kbob/MinimumViableSynth/Front Panel/archive/bob-synth-full-somevec-0.4.pdf

### Filter

### Filter Envelope

### Amp Envelope

### LFO 1

Assign Amount Speed

### LFO 2

Assign Amount Speed

### Controllers

Velocity
Mod Wheel
Aftertouch
Other
Assign Amount

### Oscillator 1

Amount Pitch Width

### Oscillator 2

Amount Pitch Width

### Noise

White
Pink
Red
Amount

### Mix

Mix
Ring Mod
Hard Sync

# Minimum Viable Synth

Low Pass
High Pass
Off
Key Track Drive Resonance Cutoff

### Envelope 1

Release Sustain Decay Attack Amount Assign

Release Sustain Decay Attack Amount

### Amp

Release Sustain Decay Attack Master Volume
