kbob/MinimumViableSynth/Front Panel/archive/bob-synth-both-0.1.pdf

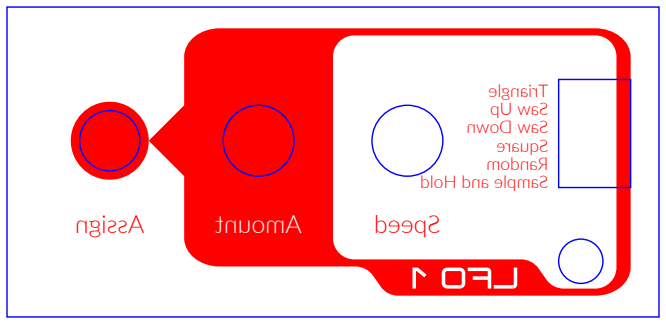
[picture p4: figure]
LFO 1; Triangle Saw Up Saw Down Square Random Sample and Hold; Assign Amount Speed
