kbob/MinimumViableSynth/Front Panel/archive/bob-synth-detail-both-0.1.pdf

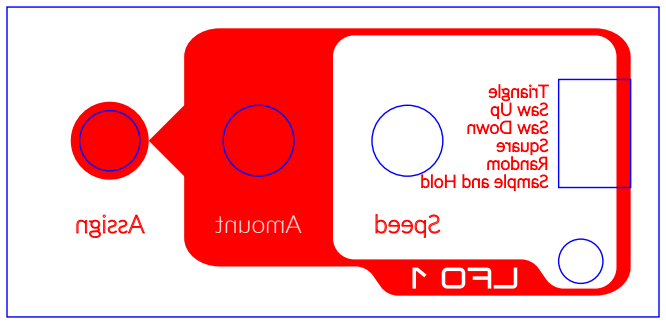
[picture p5: figure]
LFO 1; Triangle Saw Up Saw Down Square Random Sample and Hold; Assign Amount Speed
