kbob/MinimumViableSynth/Front Panel/archive/bob-synth-engrave-0.2.pdf

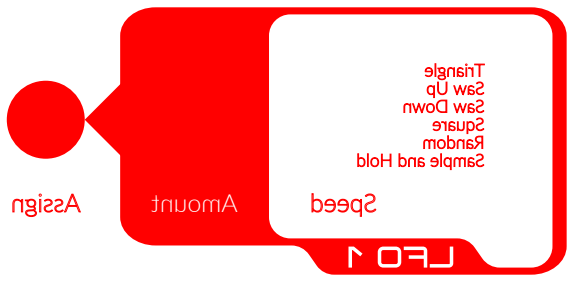
[picture p6: figure]
LFO 1; Triangle Saw Up Saw Down Square Random Sample and Hold; Assign Amount Speed
