kbob/MinimumViableSynth/Front Panel/archive/bob-synth-detail-all-0.3.pdf

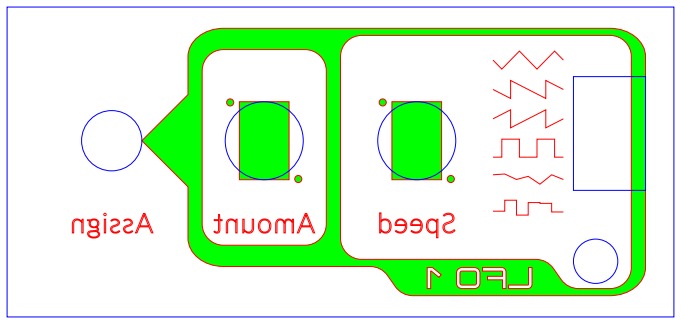
[picture p12: figure]
LFO 1; Assign Amount Speed
