kbob/MinimumViableSynth/Front Panel/archive/bob-synth-detail-allvec-0.3.pdf

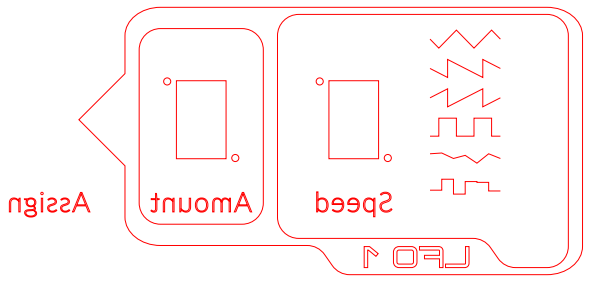
[picture p13: figure]
LFO 1; Assign Amount Speed
