kbob/MinimumViableSynth/Front Panel/archive/bob-synth-detail-art-0.3.pdf

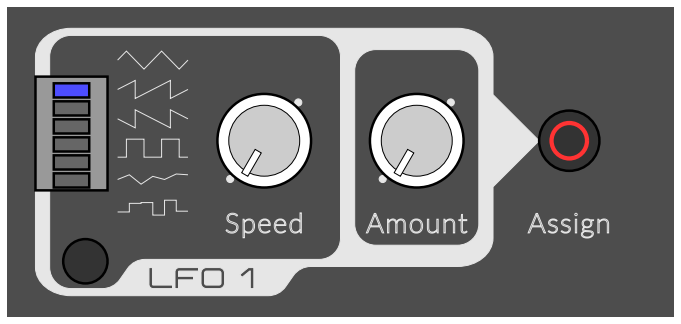
[picture p14: figure]
LFO 1; Speed; Amount; Assign
