kbob/MinimumViableSynth/Front Panel/archive/bob-synth-detail-cut-0.3.pdf

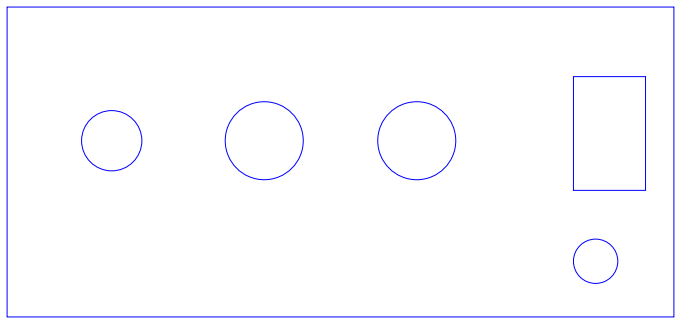
[picture p15: figure]
