kbob/MinimumViableSynth/Front Panel/archive/bob-synth-detail-engrave-0.3.pdf

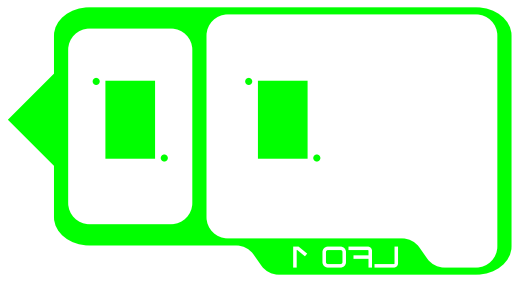
[picture p16: figure]
LFO 1; Assign Amount Speed
