kbob/MinimumViableSynth/Front Panel/archive/bob-synth-cut-0.2.pdf

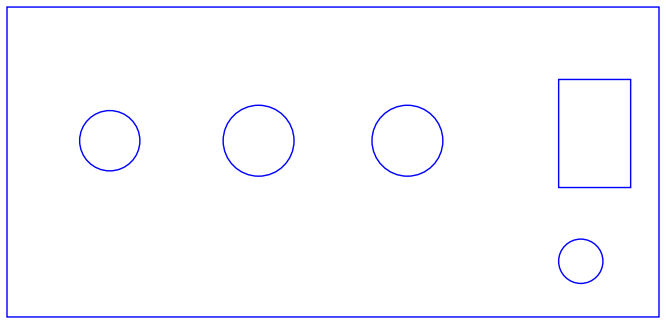
[picture p17: figure]
