kbob/MinimumViableSynth/Front Panel/archive/bob-synth-full-cut-0.3.pdf

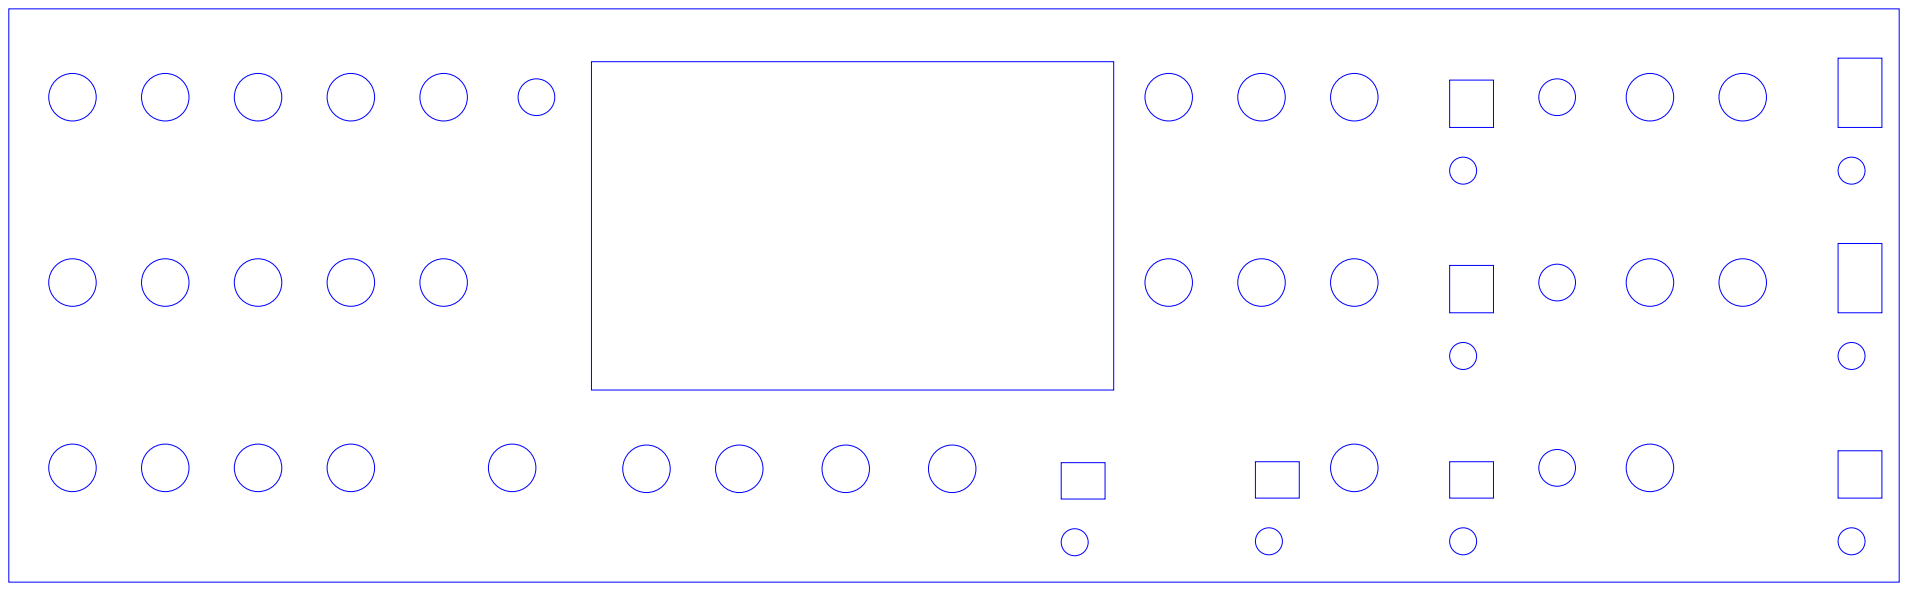
[picture p25: page 1]
