kbob/MinimumViableSynth/Firmware/Master/src/spi-proto.c

#include "spi-proto.h"

#include <assert.h>
#include <stdio.h>
#include <string.h>

#include <libopencm3/cm3/cortex.h>
#include <libopencm3/cm3/nvic.h>

#include "anim.h"
#include "config.h"
#include "delay.h"
#include "spi.h"
#include "state.h"
#include "systick.h"

#define MAX_SPI_PACKET_SIZE 32

static const uint8_t STX = '\02';
static const uint8_t ETX = '\03';
static const uint8_t SYN = '\26';

// active_modules is a hack to allow turning the synth on one module at a time.
static const size_t active_modules[] = {
    M_LFO1,
    M_LFO2,
    M_CTLRS,
    M_OSC1,
    M_OSC2,
    M_NOIS,
    M_MIX,
    // M_FILT,
    // M_ENV1,
    // M_ENV2,
    // M_ENV3,
};
static const size_t active_module_count = (&active_modules)[1] - active_modules;

typedef uint8_t spi_buf[MAX_SPI_PACKET_SIZE];

typedef enum SPI_state {
    SS_IDLE,
    SS_START,
    SS_ACTIVE,
    SS_GROUP_DONE,
    SS_POSTPROCESSING,
} SPI_state;

typedef struct SPI_stats {
    uint32_t ok_count[MODULE_COUNT];
    uint32_t fail_count[MODULE_COUNT];
    uint32_t skip_count;
} SPI_stats;

// XXX move this where other drivers can use it.
#define DMA_SECTION __attribute((section(".system_ram")))
//#define DMA_SECTION

static volatile SPI_state sp_state;
static volatile int current_grp_idx;
static spi_buf outgoing_packets[MODULE_COUNT] DMA_SECTION;
static spi_buf incoming_packets[MODULE_COUNT] DMA_SECTION;
static slave_state slave_states[MODULE_COUNT];
static SPI_stats stats;
static SPI_slave_state_handler *slave_state_handler;
static void *handler_data;

static void module_to_spi(size_t   module_index,
                          uint8_t *spi_group_out,
                          uint8_t *spi_bus_out)
{
    assert(module_index < MODULE_COUNT);
    const module_config *mcp = &sc.sc_modules[module_index];
    if (spi_group_out)
        *spi_group_out = mcp->mc_SPI_group;
    if (spi_bus_out)
        *spi_bus_out = mcp->mc_SPI_bus;
}

size_t spi_to_module(int spi_group, int spi_bus)
{
    static size_t spi2mod[SPI_GROUP_COUNT][SPI_BUS_RANGE];
    static bool initialized;

    if (!initialized) {
        for (size_t i = 0; i < MODULE_COUNT; i++) {
            uint8_t grp, bus;
            module_to_spi(i, &grp, &bus);
            spi2mod[grp][bus] = i;
        }
        initialized = true;
    }
    assert(0 <= spi_group && spi_group < SPI_GROUP_COUNT);
    assert(0 <= spi_bus && spi_bus < SPI_BUS_RANGE);
    return spi2mod[spi_group][spi_bus];
}

int active_spi_groups(uint8_t index)
{
    static uint8_t active_groups[SPI_GROUP_COUNT];
    static size_t active_group_count;

    if (!active_group_count) {
        bool active[SPI_GROUP_COUNT];
        memset(active, 0, sizeof active);
        for (size_t i = 0; i < active_module_count; i++) {
            uint8_t grp, bus;
            module_to_spi(active_modules[i], &grp, &bus);
            active[grp] = true;
        }
        for (size_t g = 0; g < SPI_GROUP_COUNT; g++)
            if (active[g])
                active_groups[active_group_count++] = g;
    }

    if (index < active_group_count)
        return active_groups[index];
    else
        return NO_GROUP;
}

int active_spi_buses(uint8_t group, uint8_t index)
{
    static uint8_t active_buses[SPI_GROUP_COUNT][SPI_BUS_COUNT];
    static size_t active_bus_count[SPI_GROUP_COUNT];
    static bool initialized;

    if (!initialized) {
        bool active[SPI_GROUP_COUNT][SPI_BUS_RANGE];
        memset(active, 0, sizeof active);
        for (size_t i = 0; i < active_module_count; i++) {
            uint8_t grp, bus;
            module_to_spi(active_modules[i], &grp, &bus);
            active[grp][bus] = true;
        }
        for (size_t g = 0; g < SPI_GROUP_COUNT; g++)
            for (size_t b = 0; b < SPI_BUS_RANGE; b++)
                if (active[g][b]) {
                    assert(active_bus_count[g] < SPI_BUS_COUNT);
                    active_buses[g][active_bus_count[g]++] = b;
                }
        initialized = true;
    }

    if (group >= SPI_GROUP_COUNT)
        return NO_GROUP;
    if (index < active_bus_count[group])
        return active_buses[group][index];
    else
        return NO_BUS;
}

static uint16_t fletcher16(const uint8_t *p, size_t count)
{
    uint16_t sum = 0;
    uint16_t sum2 = 0;
    for (size_t i = 0; i < count; i++) {
        sum += p[i];
        if (sum >= 255)
            sum -= 255;
        sum2 += sum;
        if (sum2 >= 255)
            sum2 -= 255;
    }
    return sum2 << 8 | sum;
}

// MOSI message format
//
//   STX : 1 byte
//   config 0 : 1 byte
//     bit 0:      c1 = nonzero if choice one lit
//     bit 1:      c2 = nonzero if choice two lit
//     bit 2:      c3 = nonzero if choice three lit
//     bit 3:      c4 = nonzero if choice four lit
//     bit 4:      c5 = nonzero if choice five lit
//     bit 5:      c6 = nonzero if choice six lit
//     bit 6:       (not used)
//     bit 7:      ap = nonzero if assign LED lit
//   config 1: 1 byte
//     bits 0-2:   np = number of pixels
//     bits 3-5:   na = number of analog inputs
//     bits 6-7:   unused
//   choice LED pwm: 1 byte per lit choice
//   assign LED pwm: 1 byte
//   pixels: 3 * np bytes
//     1st: title
//     2nd - np'th: knobs
//     red, green, blue order
//   checksum : 2 bytes
//   ETX : 1 byte

static size_t assemble_outgoing_packet(spi_buf packet, size_t module_index)
{
    const module_config *mcp = &sc.sc_modules[module_index];
    const module_state *msp = &ss.ss_modules[module_index];

    // These variables are copied into the packet.
    uint8_t cfg0 = 0;
    uint8_t cfg1 = 0;
    uint8_t pwm[MAX_CHOICES + MAX_ASSIGNS];
    size_t pwm_count = 0;
    uint8_t pixels[MAX_PIXELS][3];
    size_t pixel_count = 0;

    // Collect the info.
    if (mcp->mc_has_choice) {
        uint8_t first = 6 - mcp->mc_choice.cc_count;
        cfg0 |= 1 << (first + msp->ms_choice.cs_value);
        pwm[pwm_count++] = anim_choice_brightness(module_index);
    }

    if (mcp->mc_has_assign) {
        cfg0 |= 1 << 7;
        pwm[pwm_count++] = anim_assign_brightness(module_index);
    }
    
    packed_RGB rgb = anim_module_color(module_index);
    uint8_t pix = mcp->mc_LED;
    pixels[pix][0] = rgb >> 16 & 0xFF;
    pixels[pix][1] = rgb >>  8 & 0xFF;
    pixels[pix][2] = rgb >>  0 & 0xFF;

    if (mcp->mc_flags & MCF_CTLRS)
        pixel_count = 2;
    else
        pixel_count = 1 + mcp->mc_knob_count;
    cfg1 = pixel_count | mcp->mc_knob_count << 3;
    
    for (size_t ki = 0; ki < mcp->mc_knob_count; ki++) {
        const knob_config *kcp = &mcp->mc_knobs[ki];
        if (kcp->kc_name) {     // if knob exists...
            packed_RGB rgb = anim_knob_color(module_index, ki);
            uint8_t pix = kcp->kc_LED;
            pixels[pix][0] = rgb >> 16 & 0xFF;
            pixels[pix][1] = rgb >>  8 & 0xFF;
            pixels[pix][2] = rgb >>  0 & 0xFF;
        }
    }

    // Assemble the packet.
    uint8_t *p = packet;
    *p++ = STX;
    *p++ = cfg0;
    *p++ = cfg1;
    for (size_t i = 0; i < pwm_count; i++)
        *p++ = pwm[i];
    for (size_t i = 0; i < pixel_count; i++) {
        *p++ = pixels[i][0];
        *p++ = pixels[i][1];
        *p++ = pixels[i][2];
    }
    uint16_t cksum = fletcher16(packet + 1, p - packet - 1);
    *p++ = cksum >> 8;
    *p++ = cksum & 0xFF;
    *p++ = ETX;
    *p++ = SYN;
    assert(p - packet <= MAX_SPI_PACKET_SIZE);

    return p - packet;
}

// MISO message format
//
//   STX : 1 byte
//   switches: 1 byte
//     bit 0: c0 clicked
//     bit 1: assign clicked
//     bit 2: destination button 1 clicked
//     bit 3: destination button 2 clicked
//     bit 4: destination button 3 clicked
//     bit 5: destination button 4 clicked
//   analog: 1 byte
//     bit 0: analog 1 changed
//     bit 1: analog 2 changed
//     bit 2: analog 3 changed
//     bit 3: analog 4 changed
//     bit 4: analog 5 changed
//   analog values:  1 byte per changed value
//   checksum : 2 bytes
//   ETX : 1 byte

static bool check_buttons(uint8_t button_mask, size_t module_index)
{
    const module_config *mod = &sc.sc_modules[module_index];
    if ((button_mask & SBB_CHOICE) && !mod->mc_has_choice)
        return false;
    if ((button_mask & SBB_ASSIGN) && !mod->mc_has_assign)
        return false;
    for (size_t i = mod->mc_knob_count; i < MAX_KNOBS; i++)
        if ((button_mask & 1 << (i + 2)))
            return false;
    return true;
}

static bool check_analog(uint8_t analog_mask, size_t module_index)
{
    const module_config *mod = &sc.sc_modules[module_index];
    for (int i = 0; i < MAX_KNOBS; i++)
        if (analog_mask & (1 << i) &&
            (i >= mod->mc_knob_count || !mod->mc_knobs[i].kc_has_button))
            return false;
    return true;
}

static bool parse_incoming_packet(spi_buf const packet,
                                  size_t        count,
                                  size_t        module_index,
                                  slave_state  *state_out)
{
#if 0
    #define PARSE_DBG(fmt, ...)                             \
        (printf("%s: " fmt "\n",                            \
                sc.sc_modules[module_index].mc_name,        \
                __VA_ARGS__))
#else
    #define PARSE_DBG(fmt, ...) ((void)0)
#endif

    if (count < 6) {
        PARSE_DBG("count = %u < 6, fail", count);
        return false;
    }
    if (packet[0] != STX) {
        PARSE_DBG("packet[0] = %#o != STX", packet[0]);
        return false;
    }
    size_t len = 6;             // 6 bytes: STX bmask amask chk chk ETX
    uint8_t bmask = packet[1];
    uint8_t amask = packet[2];
    for (uint8_t i = 1; i; i <<= 1)
        if (amask & i)
            len++;
    if (count < len) {
        PARSE_DBG("received %u bytes, expected %u bytes", count, len);
        return false;
    }
    uint16_t rx_chk = (uint16_t)packet[len - 3] << 8 | packet[len - 2];
    uint16_t cc_chk = fletcher16(packet + 1, len - 4);
    if (rx_chk != cc_chk) {
        PARSE_DBG("chk: got %#x, not %#x", rx_chk, cc_chk);
        return false;
    }
    if (packet[len - 1] != ETX) {
        PARSE_DBG("packet[%u] = %#o, expected ETX", len - 1, packet[len - 1]);
        return false;
    }
    if (!check_buttons(bmask, module_index)) {
        PARSE_DBG("bmask %#x invalid", bmask);
        return false;
    }
    if (!check_analog(amask, module_index)) {
        PARSE_DBG("amask %#x invalid", amask);
        return false;
    }

    // Populate the slave_state.
    state_out->ss_is_valid = true;
    state_out->ss_buttons = bmask;
    state_out->ss_analog_mask = amask;
    const uint8_t *p = packet + 3;
    for (int i = 0; i < MAX_KNOBS; i++)
        if (amask & (1 << i))
            state_out->ss_analog_values[i] = *p++;
    return true;
}

static void start_SPI_group(int grp)
{
    spi_select_group(grp);
    delay_usec(20);
    int bus;
    for (int i = 0; (bus = active_spi_buses(grp, i)) != NO_BUS; i++) {
        size_t mod_idx = spi_to_module(grp, bus);
        size_t bytes_out =
            assemble_outgoing_packet(outgoing_packets[mod_idx], mod_idx);
        spi_start_transfer(bus,
                           outgoing_packets[mod_idx],
                           incoming_packets[mod_idx],
                           bytes_out);
    }
}

static void stop_SPI_group(int grp)
{
    int bus;
    for (int i = 0; (bus = active_spi_buses(grp, i)) != NO_BUS; i++)
        spi_finish_transfer(bus);
    delay_usec(20);
    spi_deselect_group(grp);
}

static void process_SPI_group(int grp)
{
    int bus;
    for (int i = 0; (bus = active_spi_buses(grp, i)) != NO_BUS; i++) {
        size_t mod_idx = spi_to_module(grp, bus);
        bool ok = parse_incoming_packet(incoming_packets[mod_idx],
                                        sizeof incoming_packets[mod_idx],
                                        mod_idx,
                                        &slave_states[mod_idx]);
        if (ok)
            stats.ok_count[mod_idx]++;
        else
            stats.fail_count[mod_idx]++;
    }
}

static void postprocess_SPI(void)
{
    if (slave_state_handler) {
        for (size_t i = 0; i < MODULE_COUNT; i++) {
            const slave_state *ss = &slave_states[i];
            if (ss->ss_is_valid)
                (*slave_state_handler)(i, &slave_states[i], handler_data);
        }
    }
}

// This is the main event handler for the SPI proto task.
void exti0_isr(void)
{
    switch (sp_state) {

    case SS_START:
        memset(outgoing_packets, 0, sizeof outgoing_packets);
        memset(incoming_packets, 0, sizeof incoming_packets);
        memset(slave_states, 0, sizeof slave_states);
        current_grp_idx = -1;
        anim_update(system_millis);
        /* FALLTHRU */

    case SS_GROUP_DONE:;
        // N.B., we start the next SPI group running before
        // we parse the reply messages from the current group.
        int prev_grp_idx = current_grp_idx;
        current_grp_idx++;
        int current_grp = active_spi_groups(current_grp_idx);
        if (prev_grp_idx != -1)
            stop_SPI_group(active_spi_groups(prev_grp_idx));
        if (current_grp != NO_GROUP) {
            sp_state = SS_ACTIVE;
            start_SPI_group(current_grp);
        }
        if (prev_grp_idx != -1) {
            int prev_grp = active_spi_groups(prev_grp_idx);
            process_SPI_group(prev_grp);
        }
        if (current_grp == NO_GROUP) {
            sp_state = SS_POSTPROCESSING;
            postprocess_SPI();
            sp_state = SS_IDLE;
        }
        break;

    case SS_ACTIVE:
    case SS_IDLE:
    case SS_POSTPROCESSING:
        assert(!"Unexpected SPI state");
        break;
    }
}

static void handle_systick(uint32_t millis)
{
    if (sp_state == SS_IDLE) {
        sp_state = SS_START;
        nvic_generate_software_interrupt(NVIC_EXTI0_IRQ);
    } else {
        stats.skip_count++;
    }
}

static void handle_SPI_completion(void)
{
    if (sp_state == SS_ACTIVE) {
        sp_state = SS_GROUP_DONE;
        nvic_generate_software_interrupt(NVIC_EXTI0_IRQ);
    }
}

void SPI_proto_setup(void)
{
    spi_register_completion_handler(handle_SPI_completion);
    sp_state = SS_IDLE;
    nvic_set_priority(NVIC_EXTI0_IRQ, 0xFF);
    nvic_enable_irq(NVIC_EXTI0_IRQ);
    register_systick_handler(handle_systick);
}

void SPI_proto_register_slave_state_handler(SPI_slave_state_handler *handler,
                                            void *user_data)
{
    slave_state_handler = handler;
    handler_data = user_data;
}

void SPI_proto_report_and_clear_stats(void)
{
    bool interrupts_are_masked = cm_is_masked_interrupts();
    cm_disable_interrupts();

    SPI_stats tmp = stats;
    memset(&stats, 0, sizeof stats);

    if (!interrupts_are_masked)
        cm_enable_interrupts();

    printf("   OK  fail module\n");
    for (size_t i = 0; i < MODULE_COUNT; i++) {
        uint32_t ok = tmp.ok_count[i];
        uint32_t fail = tmp.fail_count[i];
        if (!ok && !fail)
            continue;
        const char *mod_name = sc.sc_modules[i].mc_name;
        printf("%5lu %5lu %s\n", ok, fail, mod_name);
    }
    if (tmp.skip_count)
        printf("skipped %lu\n", tmp.skip_count);
    printf("\n");
}
