kbob/MinimumViableSynth/Firmware/Master/src/usb-midi.c

#include "usb-midi.h"

// Based heavily on usbmidi.c in libopencm3-examples, which is
//  * Copyright (C) 2014 Daniel Thompson <daniel@redfelineninja.org.uk>
//  * Copyright (C) 2015 Piotr Esden-Tempski <piotr@esden.net>
// and licensed under the LGPL.

/*
 * All references in this file come from Universal Serial Bus Device Class
 * Definition for MIDI Devices, release 1.0.
 */

#include <assert.h>
#include <stdio.h>
#include <string.h>

#include <libopencm3/cm3/cortex.h>
#include <libopencm3/cm3/nvic.h>

#include <libopencm3/usb/usbd.h>
#include <libopencm3/usb/audio.h>
#include <libopencm3/usb/midi.h>

#include <libopencm3/stm32/rcc.h>

#include "gpio.h"
#include "midi-defs.h"

/*
 * Table B-1: MIDI Adapter Device Descriptor
 */
static const struct usb_device_descriptor dev = {
	.bLength = USB_DT_DEVICE_SIZE,
	.bDescriptorType = USB_DT_DEVICE,
	.bcdUSB = 0x0200,    /* was 0x0110 in Table B-1 example descriptor */
	.bDeviceClass = 0,   /* device defined at interface level */
	.bDeviceSubClass = 0,
	.bDeviceProtocol = 0,
	.bMaxPacketSize0 = 64,
	.idVendor = 0x6666,  /* Prototype product vendor ID */
	.idProduct = 0x5119, /* dd if=/dev/random bs=2 count=1 | hexdump */
	.bcdDevice = 0x0100,
	.iManufacturer = 1,  /* index to string desc */
	.iProduct = 2,       /* index to string desc */
	.iSerialNumber = 0,
	.bNumConfigurations = 1,
};

/*
 * Midi specific endpoint descriptors.
 */
static const struct usb_midi_endpoint_descriptor midi_bulk_endp[] = {{
	/* Table B-12: MIDI Adapter Class-specific Bulk OUT Endpoint
	 * Descriptor
	 */
	.head = {
		.bLength = sizeof(struct usb_midi_endpoint_descriptor),
		.bDescriptorType = USB_AUDIO_DT_CS_ENDPOINT,
		.bDescriptorSubType = USB_MIDI_SUBTYPE_MS_GENERAL,
		.bNumEmbMIDIJack = 1,
	},
	.jack[0] = {
		.baAssocJackID = 0x01,
	},
}, {
	/* Table B-14: MIDI Adapter Class-specific Bulk IN Endpoint
	 * Descriptor
	 */
	.head = {
		.bLength = sizeof(struct usb_midi_endpoint_descriptor),
		.bDescriptorType = USB_AUDIO_DT_CS_ENDPOINT,
		.bDescriptorSubType = USB_MIDI_SUBTYPE_MS_GENERAL,
		.bNumEmbMIDIJack = 1,
	},
	.jack[0] = {
		.baAssocJackID = 0x03,
	},
} };

/*
 * Standard endpoint descriptors
 */
static const struct usb_endpoint_descriptor bulk_endp[] = {{
	/* Table B-11: MIDI Adapter Standard Bulk OUT Endpoint Descriptor */
	.bLength = USB_DT_ENDPOINT_SIZE,
	.bDescriptorType = USB_DT_ENDPOINT,
	.bEndpointAddress = 0x01,
	.bmAttributes = USB_ENDPOINT_ATTR_BULK,
	.wMaxPacketSize = 0x40,
	.bInterval = 0x00,

	.extra = &midi_bulk_endp[0],
	.extralen = sizeof(midi_bulk_endp[0])
}, {
	.bLength = USB_DT_ENDPOINT_SIZE,
	.bDescriptorType = USB_DT_ENDPOINT,
	.bEndpointAddress = 0x81,
	.bmAttributes = USB_ENDPOINT_ATTR_BULK,
	.wMaxPacketSize = 0x40,
	.bInterval = 0x00,

	.extra = &midi_bulk_endp[1],
	.extralen = sizeof(midi_bulk_endp[1])
} };

/*
 * Table B-4: MIDI Adapter Class-specific AC Interface Descriptor
 */
static const struct {
	struct usb_audio_header_descriptor_head header_head;
	struct usb_audio_header_descriptor_body header_body;
} __attribute__((packed)) audio_control_functional_descriptors = {
	.header_head = {
		.bLength = sizeof(struct usb_audio_header_descriptor_head) +
			   1 * sizeof(struct usb_audio_header_descriptor_body),
		.bDescriptorType = USB_AUDIO_DT_CS_INTERFACE,
		.bDescriptorSubtype = USB_AUDIO_TYPE_HEADER,
		.bcdADC = 0x0100,
		.wTotalLength =
			   sizeof(struct usb_audio_header_descriptor_head) +
			   1 * sizeof(struct usb_audio_header_descriptor_body),
		.binCollection = 1,
	},
	.header_body = {
		.baInterfaceNr = 0x01,
	},
};

/*
 * Table B-3: MIDI Adapter Standard AC Interface Descriptor
 */
static const struct usb_interface_descriptor audio_control_iface[] = {{
	.bLength = USB_DT_INTERFACE_SIZE,
	.bDescriptorType = USB_DT_INTERFACE,
	.bInterfaceNumber = 0,
	.bAlternateSetting = 0,
	.bNumEndpoints = 0,
	.bInterfaceClass = USB_CLASS_AUDIO,
	.bInterfaceSubClass = USB_AUDIO_SUBCLASS_CONTROL,
	.bInterfaceProtocol = 0,
	.iInterface = 0,

	.extra = &audio_control_functional_descriptors,
	.extralen = sizeof(audio_control_functional_descriptors)
} };

/*
 * Class-specific MIDI streaming interface descriptor
 */
static const struct {
	struct usb_midi_header_descriptor header;
	struct usb_midi_in_jack_descriptor in_embedded;
	struct usb_midi_in_jack_descriptor in_external;
	struct usb_midi_out_jack_descriptor out_embedded;
	struct usb_midi_out_jack_descriptor out_external;
} __attribute__((packed)) midi_streaming_functional_descriptors = {
	/* Table B-6: Midi Adapter Class-specific MS Interface Descriptor */
	.header = {
		.bLength = sizeof(struct usb_midi_header_descriptor),
		.bDescriptorType = USB_AUDIO_DT_CS_INTERFACE,
		.bDescriptorSubtype = USB_MIDI_SUBTYPE_MS_HEADER,
		.bcdMSC = 0x0100,
		.wTotalLength = sizeof(midi_streaming_functional_descriptors),
	},
	/* Table B-7: MIDI Adapter MIDI IN Jack Descriptor (Embedded) */
	.in_embedded = {
		.bLength = sizeof(struct usb_midi_in_jack_descriptor),
		.bDescriptorType = USB_AUDIO_DT_CS_INTERFACE,
		.bDescriptorSubtype = USB_MIDI_SUBTYPE_MIDI_IN_JACK,
		.bJackType = USB_MIDI_JACK_TYPE_EMBEDDED,
		.bJackID = 0x01,
		.iJack = 0x00,
	},
	/* Table B-8: MIDI Adapter MIDI IN Jack Descriptor (External) */
	.in_external = {
		.bLength = sizeof(struct usb_midi_in_jack_descriptor),
		.bDescriptorType = USB_AUDIO_DT_CS_INTERFACE,
		.bDescriptorSubtype = USB_MIDI_SUBTYPE_MIDI_IN_JACK,
		.bJackType = USB_MIDI_JACK_TYPE_EXTERNAL,
		.bJackID = 0x02,
		.iJack = 0x00,
	},
	/* Table B-9: MIDI Adapter MIDI OUT Jack Descriptor (Embedded) */
	.out_embedded = {
		.head = {
			.bLength = sizeof(struct usb_midi_out_jack_descriptor),
			.bDescriptorType = USB_AUDIO_DT_CS_INTERFACE,
			.bDescriptorSubtype = USB_MIDI_SUBTYPE_MIDI_OUT_JACK,
			.bJackType = USB_MIDI_JACK_TYPE_EMBEDDED,
			.bJackID = 0x03,
			.bNrInputPins = 1,
		},
		.source[0] = {
			.baSourceID = 0x02,
			.baSourcePin = 0x01,
		},
		.tail = {
			.iJack = 0x00,
		}
	},
	/* Table B-10: MIDI Adapter MIDI OUT Jack Descriptor (External) */
	.out_external = {
		.head = {
			.bLength = sizeof(struct usb_midi_out_jack_descriptor),
			.bDescriptorType = USB_AUDIO_DT_CS_INTERFACE,
			.bDescriptorSubtype = USB_MIDI_SUBTYPE_MIDI_OUT_JACK,
			.bJackType = USB_MIDI_JACK_TYPE_EXTERNAL,
			.bJackID = 0x04,
			.bNrInputPins = 1,
		},
		.source[0] = {
			.baSourceID = 0x01,
			.baSourcePin = 0x01,
		},
		.tail = {
			.iJack = 0x00,
		},
	},
};

/*
 * Table B-5: MIDI Adapter Standard MS Interface Descriptor
 */
static const struct usb_interface_descriptor midi_streaming_iface[] = {{
	.bLength = USB_DT_INTERFACE_SIZE,
	.bDescriptorType = USB_DT_INTERFACE,
	.bInterfaceNumber = 1,
	.bAlternateSetting = 0,
	.bNumEndpoints = 2,
	.bInterfaceClass = USB_CLASS_AUDIO,
	.bInterfaceSubClass = USB_AUDIO_SUBCLASS_MIDISTREAMING,
	.bInterfaceProtocol = 0,
	.iInterface = 0,

	.endpoint = bulk_endp,

	.extra = &midi_streaming_functional_descriptors,
	.extralen = sizeof(midi_streaming_functional_descriptors)
} };

static const struct usb_interface ifaces[] = {{
	.num_altsetting = 1,
	.altsetting = audio_control_iface,
}, {
	.num_altsetting = 1,
	.altsetting = midi_streaming_iface,
} };

/*
 * Table B-2: MIDI Adapter Configuration Descriptor
 */
static const struct usb_config_descriptor config = {
	.bLength = USB_DT_CONFIGURATION_SIZE,
	.bDescriptorType = USB_DT_CONFIGURATION,
	.wTotalLength = 0, /* can be anything, it is updated automatically
			      when the usb code prepares the descriptor */
	.bNumInterfaces = 2, /* control and data */
	.bConfigurationValue = 1,
	.iConfiguration = 0,
	.bmAttributes = 0x80, /* bus powered */
	.bMaxPower = 0x32,

	.interface = ifaces,
};

static const char *usb_strings[] = {
	"kbob",
	"Minimum Viable MIDI",
};

static usbd_device *usbd_dev;

/* Buffer to be used for control requests. */
static uint8_t usbd_control_buffer[128];

/* SysEx identity message, preformatted with correct USB framing information */
static const uint8_t sysex_identity[] = {
	0x04,	/* USB Framing (3 byte SysEx) */
	0xf0,	/* SysEx start */
	0x7e,	/* non-realtime */
	0x00,	/* Channel 0 */
	0x04,	/* USB Framing (3 byte SysEx) */
	0x7d,	/* Educational/prototype manufacturer ID */
	0x66,	/* Family code (byte 1) */
	0x66,	/* Family code (byte 2) */
	0x04,	/* USB Framing (3 byte SysEx) */
	0x51,	/* Model number (byte 1) */
	0x19,	/* Model number (byte 2) */
	0x00,	/* Version number (byte 1) */
	0x04,	/* USB Framing (3 byte SysEx) */
	0x00,	/* Version number (byte 2) */
	0x01,	/* Version number (byte 3) */
	0x00,	/* Version number (byte 4) */
	0x05,	/* USB Framing (1 byte SysEx) */
	0xf7,	/* SysEx end */
	0x00,	/* Padding */
	0x00,	/* Padding */
};

static const gpio_pin usb_id_pin = {
    .gp_port = GPIOB,
    .gp_pin  = GPIO12,
    .gp_mode = GPIO_MODE_AF,
    .gp_pupd = GPIO_PUPD_NONE,
    .gp_af   = GPIO_AF12,
};

static const gpio_pin usb_dm_pin = {
    .gp_port = GPIOB,
    .gp_pin  = GPIO14,
    .gp_mode = GPIO_MODE_AF,
    .gp_pupd = GPIO_PUPD_NONE,
    .gp_af   = GPIO_AF12,
};

static const gpio_pin usb_dp_pin = {
    .gp_port = GPIOB,
    .gp_pin  = GPIO15,
    .gp_mode = GPIO_MODE_AF,
    .gp_pupd = GPIO_PUPD_NONE,
    .gp_af   = GPIO_AF12,
};

typedef uint8_t usb_midi_packet[4];

static void usbmidi_data_rx_cb(usbd_device *usbd_dev, uint8_t ep)
{
	(void)ep;

	char buf[64];
	int len = usbd_ep_read_packet(usbd_dev, 0x01, buf, 64);

	/* This implementation treats any message from the host as a SysEx
	 * identity request. This works well enough providing the host
	 * packs the identify request in a single 8 byte USB message.
	 */
	if (len) {
		while (usbd_ep_write_packet(usbd_dev, 0x81, sysex_identity,
					    sizeof(sysex_identity)) == 0);
	}

	gpio_toggle(GPIOC, GPIO5);
}

static void usb_midi_set_config(usbd_device *usbd_dev, uint16_t wValue)
{
	(void)wValue;

	usbd_ep_setup(usbd_dev, 0x01, USB_ENDPOINT_ATTR_BULK, 64,
			usbmidi_data_rx_cb);
	usbd_ep_setup(usbd_dev, 0x81, USB_ENDPOINT_ATTR_BULK, 64, NULL);
}

void usb_midi_setup(void)
{
    // Clock
    rcc_periph_clock_enable(RCC_OTGHS);

    // GPIO
    gpio_init_pin(&usb_id_pin);
    gpio_init_pin(&usb_dm_pin);
    gpio_init_pin(&usb_dp_pin);

    // USB
    usbd_dev = usbd_init(&otghs_usb_driver, &dev, &config,
                         usb_strings, 2,
                         usbd_control_buffer, sizeof(usbd_control_buffer));

    usbd_register_set_config_callback(usbd_dev, usb_midi_set_config);
}

void usb_midi_poll(void)
{
    usbd_poll(usbd_dev);
}

void usb_midi_send_message(uint8_t const *msg, size_t size)
{
    if (!size)
        return;
    uint8_t status = msg[0];
    assert(status & 0x80);
    uint8_t status_hi = status & 0xF0;
    if (status_hi == SystemCommon) {
        // This is a System Common message.
        assert(!"Write me!");
    } else {
        // This is a Channel Voice message.
        uint8_t cin = status_hi >> 4;
        uint8_t cn = 0;         // cable number 0
        usb_midi_packet pkt;
        if (status_hi == ProgramChange || status_hi == ChannelPressure) {
            // Two-byte message
            assert(size == 2);
            pkt[0] = cn << 4 | cin;
            pkt[1] = status;
            pkt[2] = msg[1];
            pkt[3] = 0;
        } else {
            // Three-byte message
            assert(size = 3);
            pkt[0] = cn << 4 | cin;
            pkt[1] = status;
            pkt[2] = msg[1];
            pkt[3] = msg[2];
        }
        while (usbd_ep_write_packet(usbd_dev, 0x81, pkt, sizeof pkt) == 0)
            continue;
    }
    return;
}

typedef struct usb_midi_stats {
} usb_midi_stats;

static usb_midi_stats stats;

void usb_midi_proto_report_and_clear_stats(void)
{
    bool interrupts_are_masked = cm_is_masked_interrupts();
    cm_disable_interrupts();

    usb_midi_stats tmp = stats;
    memset(&stats, 0, sizeof stats);

    if (!interrupts_are_masked)
        cm_enable_interrupts();

    printf("   OK  fail module\n");
    tmp = tmp;
}
