kbob/MinimumViableSynth/Firmware/Master/src/spi.c

#include "spi.h"

#include <assert.h>
#include <stdbool.h>

#include <libopencm3/cm3/cortex.h>
#include <libopencm3/cm3/nvic.h>
#include <libopencm3/stm32/dma.h>
#include <libopencm3/stm32/rcc.h>
#include <libopencm3/stm32/spi.h>

#include "gpio.h"

// We use SPI buses 1, 3, 4, and 5.
// SPI bus 5 is also used for the LCD panel and the MEMS device.
// Pins PC1 and PC2 are SPI chip select pins for LCD and MEMS devices,
// so they must be held high.

// Pins
//
//  SPI 1
//    SCK   PA5   AF5
//    MISO  PB4   AF5
//    MOSI  PA7   AF5
//
//  SPI 3
//    SCK   PB3   AF6
//    MISO  PC11  AF6
//    MOSI  PC12  AF6
//
//  SPI 4
//    SCK   PE2   AF5
//    MISO  PE5   AF5
//    MOSI  PE6   AF5
//
//  SPI 5
//    SCK   PF7   AF5
//    MISO  PF8   AF5
//    MOSI  PF9   AF5

// There are three or four SPI groups.
// Each group uses all four SPI buses and is enabled by a single slave
// select line.  The nSS lines are controlled by software.
//
//    Group A: PB7
//    Group B: PE3
//    Group C: PC3
//    Group D: PC8

// Each active DMA requires a controller/stream/channel triple.
// Each controller/stream can only have a single channel active at a time.
//
//   SPI 1 RX: 2/0/3, 2/2/3
//   SPI 1 TX: 2/3/3, 2/5/3
//
//   SPI 3 RX: 1/0/0, 1/2/0
//   SPI 3 TX: 1/5/0, 1/7/0
//
//   SPI 4 RX: 2/0/4, 2/3/5
//   SPI 4 TX: 2/1/4, 2/4/5
//
//   SPI 5 RX: 2/3/2, 2/5/7
//   SPI 5 TX: 2/4/2, 2/6/7
//
// There is only one way to activate all eight channels simultaneously
// without conflicts.  See the spi_config definitions.

typedef struct DMA_channel {
    uint32_t dc_dma;
    uint8_t  dc_stream;
    uint8_t  dc_channel;
} DMA_channel;

typedef struct spi_config {
    uint32_t    sc_reg_base;
    gpio_pin    sc_sck;
    gpio_pin    sc_miso;
    gpio_pin    sc_mosi;
    DMA_channel sc_rx_dma;
    DMA_channel sc_tx_dma;
} spi_config;

static const spi_config spi1_config = {
    .sc_reg_base   = SPI1_BASE,
    .sc_sck        = {
        .gp_port   =     GPIOA,
        .gp_pin    =     GPIO5,
        .gp_mode   =     GPIO_MODE_AF,
        .gp_pupd   =     GPIO_PUPD_PULLDOWN,
        .gp_af     =     GPIO_AF5,
        .gp_ospeed =     GPIO_OSPEED_50MHZ,
    },
    .sc_miso       = {
        .gp_port   =     GPIOB,
        .gp_pin    =     GPIO4,
        .gp_mode   =     GPIO_MODE_AF,
        .gp_af     =     GPIO_AF5,
        .gp_pupd   =     GPIO_PUPD_PULLUP,
        .gp_ospeed =     GPIO_OSPEED_50MHZ,
    },
    .sc_mosi       = {
        .gp_port   =     GPIOA,
        .gp_pin    =     GPIO7,
        .gp_mode   =     GPIO_MODE_AF,
        .gp_pupd   =     GPIO_PUPD_NONE,
        .gp_af     =     GPIO_AF5,
        .gp_ospeed =     GPIO_OSPEED_50MHZ,
    },
    .sc_rx_dma     = { DMA2,  DMA_STREAM2, 3 },
    .sc_tx_dma     = { DMA2,  DMA_STREAM3, 3 },
};

static const spi_config spi3_config = {
    .sc_reg_base   = SPI3_BASE,
    .sc_sck        = {
        .gp_port   =     GPIOB,
        .gp_pin    =     GPIO3,
        .gp_mode   =     GPIO_MODE_AF,
        .gp_pupd   =     GPIO_PUPD_PULLDOWN,
        .gp_af     =     GPIO_AF6,
        .gp_ospeed =     GPIO_OSPEED_50MHZ,
    },
    .sc_miso       = {
        .gp_port   =     GPIOC,
        .gp_pin    =     GPIO11,
        .gp_mode   =     GPIO_MODE_AF,
        .gp_pupd   =     GPIO_PUPD_PULLUP,
        .gp_af     =     GPIO_AF6,
        .gp_ospeed =     GPIO_OSPEED_50MHZ,
    },
    .sc_mosi       = {
        .gp_port   =     GPIOC,
        .gp_pin    =     GPIO12,
        .gp_mode   =     GPIO_MODE_AF,
        .gp_pupd   =     GPIO_PUPD_NONE,
        .gp_af     =     GPIO_AF6,
        .gp_ospeed =     GPIO_OSPEED_50MHZ,
    },
    .sc_rx_dma     = { DMA1,  DMA_STREAM0, 0 },
    .sc_tx_dma     = { DMA1,  DMA_STREAM5, 0 },
};

static const spi_config spi4_config = {
    .sc_reg_base   = SPI4_BASE,
    .sc_sck        = {
        .gp_port   =     GPIOE,
        .gp_pin    =     GPIO2,
        .gp_mode   =     GPIO_MODE_AF,
        .gp_pupd   =     GPIO_PUPD_PULLDOWN,
        .gp_af     =     GPIO_AF5,
        .gp_ospeed =     GPIO_OSPEED_50MHZ,
    },
    .sc_miso       = {
        .gp_port   =     GPIOE,
        .gp_pin    =     GPIO5,
        .gp_mode   =     GPIO_MODE_AF,
        .gp_pupd   =     GPIO_PUPD_PULLUP,
        .gp_af     =     GPIO_AF5,
        .gp_ospeed =     GPIO_OSPEED_50MHZ,
    },
    .sc_mosi       = {
        .gp_port   =     GPIOE,
        .gp_pin    =     GPIO6,
        .gp_mode   =     GPIO_MODE_AF,
        .gp_pupd   =     GPIO_PUPD_NONE,
        .gp_af     =     GPIO_AF5,
        .gp_ospeed =     GPIO_OSPEED_50MHZ,
    },
    .sc_rx_dma     = { DMA2,  DMA_STREAM0, 4 },
    .sc_tx_dma     = { DMA2,  DMA_STREAM1, 4 },
};

static const spi_config spi5_config = {
    .sc_reg_base   = SPI5_BASE,
    .sc_sck        = {
        .gp_port   =     GPIOF,
        .gp_pin    =     GPIO7,
        .gp_mode   =     GPIO_MODE_AF,
        .gp_pupd   =     GPIO_PUPD_PULLDOWN,
        .gp_af     =     GPIO_AF5,
        .gp_ospeed =     GPIO_OSPEED_50MHZ,
    },
    .sc_miso       = {
        .gp_port   =     GPIOF,
        .gp_pin    =     GPIO8,
        .gp_mode   =     GPIO_MODE_AF,
        .gp_pupd   =     GPIO_PUPD_PULLUP,
        .gp_af     =     GPIO_AF5,
        .gp_ospeed =     GPIO_OSPEED_50MHZ,
    },
    .sc_mosi       = {
        .gp_port   =     GPIOF,
        .gp_pin    =     GPIO9,
        .gp_mode   =     GPIO_MODE_AF,
        .gp_pupd   =     GPIO_PUPD_NONE,
        .gp_af     =     GPIO_AF5,
        .gp_ospeed =     GPIO_OSPEED_50MHZ,
    },
    .sc_rx_dma     = { DMA2,  DMA_STREAM5, 7 },
    .sc_tx_dma     = { DMA2,  DMA_STREAM6, 7 },
};

static const spi_config *config_map[SPI_BUS_RANGE] = {
    NULL,
    &spi1_config,
    NULL,
    &spi3_config,
    &spi4_config,
    &spi5_config,
    NULL,
};

static const gpio_pin group_ss_pins[] = {
    {                           // Group A CS: PB7
        .gp_port  = GPIOB,
        .gp_pin   = GPIO7,
        .gp_mode  = GPIO_MODE_OUTPUT,
        .gp_level = 1,
    },
    {                           // Group B CS: PE3
        .gp_port  = GPIOE,
        .gp_pin   = GPIO3,
        .gp_mode  = GPIO_MODE_OUTPUT,
        .gp_level = 1,
    },
    {                           // Group C CS: PC3
        .gp_port  = GPIOC,
        .gp_pin   = GPIO3,
        .gp_mode  = GPIO_MODE_OUTPUT,
        .gp_level = 1,
    },
    {                           // Group D CS: PC8
        .gp_port  = GPIOC,
        .gp_pin   = GPIO8,
        .gp_mode  = GPIO_MODE_OUTPUT,
        .gp_level = 1,
    },
};
static const size_t group_count = (&group_ss_pins)[1] - group_ss_pins;

static const gpio_pin disable_cs_pins[] = {
    {
        .gp_port  = GPIOC,
        .gp_pin   = GPIO1,
        .gp_mode  = GPIO_MODE_OUTPUT,
        .gp_level = 1,
    },
    {
        .gp_port  = GPIOC,
        .gp_pin   = GPIO2,
        .gp_mode  = GPIO_MODE_OUTPUT,
        .gp_level = 1,
    },
};
static const size_t disable_cs_pin_count =
    (&disable_cs_pins)[1] - disable_cs_pins;

static volatile uint8_t active_bus_mask;
static spi_completion_handler *completion_handler;

static inline void mark_bus_inactive(uint8_t bus)
{
    active_bus_mask &= ~(1 << bus);
    if (active_bus_mask == 0 && completion_handler)
        (*completion_handler)();
}

#define WITH_INTERRUPTS_MASKED                                          \
     for (bool wim_interrupts_are_masked = cm_is_masked_interrupts(),   \
               wim_first_time = (cm_disable_interrupts(), true);        \
          wim_first_time;                                               \
          wim_interrupts_are_masked ? (void)0 : cm_enable_interrupts(), \
          wim_first_time = false)

static inline void mark_bus_active(uint8_t bus)
{
#if 0
    bool interrupts_are_masked = cm_is_masked_interrupts();
    cm_disable_interrupts();

    active_bus_mask |= 1 << bus;

    if (!interrupts_are_masked)
        cm_enable_interrupts();
#else
    WITH_INTERRUPTS_MASKED {
        active_bus_mask |= 1 << bus;
    }
#endif
}

void dma2_stream2_isr(void)
{
    dma_clear_interrupt_flags(DMA2, DMA_STREAM2, DMA_TCIF);
    uint8_t bus = 1;
    mark_bus_inactive(bus);
}

void dma1_stream0_isr(void)
{
    dma_clear_interrupt_flags(DMA1, DMA_STREAM0, DMA_TCIF);
    uint8_t bus = 3;
    mark_bus_inactive(bus);
}

void dma2_stream0_isr(void)
{
    dma_clear_interrupt_flags(DMA2, DMA_STREAM0, DMA_TCIF);
    uint8_t bus = 4;
    mark_bus_inactive(bus);
}

void dma2_stream5_isr(void)
{
    dma_clear_interrupt_flags(DMA2, DMA_STREAM5, DMA_TCIF);
    uint8_t bus = 5;
    mark_bus_inactive(bus);
}

static void spi_setup_config(const spi_config *config)
{
    // GPIO 
    gpio_init_pin(&config->sc_sck);
    gpio_init_pin(&config->sc_miso);
    gpio_init_pin(&config->sc_mosi);

    // Init SPI
    spi_init_master(config->sc_reg_base,
                    SPI_CR1_BAUDRATE_FPCLK_DIV_256,
                    SPI_CR1_CPOL_CLK_TO_0_WHEN_IDLE,
                    SPI_CR1_CPHA_CLK_TRANSITION_2,
                    SPI_CR1_DFF_8BIT,
                    SPI_CR1_MSBFIRST);
    spi_enable_rx_dma(config->sc_reg_base);
    spi_enable_tx_dma(config->sc_reg_base);
    spi_enable_ss_output(config->sc_reg_base);
}

void spi_setup(void)
{
    // Clocks.
    rcc_periph_clock_enable(RCC_SPI1);
    rcc_periph_clock_enable(RCC_SPI3);
    rcc_periph_clock_enable(RCC_SPI4);
    rcc_periph_clock_enable(RCC_SPI5);

    rcc_periph_clock_enable(RCC_DMA1);
    rcc_periph_clock_enable(RCC_DMA2);

    nvic_enable_irq(NVIC_DMA2_STREAM2_IRQ);
    nvic_enable_irq(NVIC_DMA1_STREAM0_IRQ);
    nvic_enable_irq(NVIC_DMA2_STREAM0_IRQ);
    nvic_enable_irq(NVIC_DMA2_STREAM5_IRQ);
    
    spi_setup_config(&spi1_config);
    spi_setup_config(&spi3_config);
    spi_setup_config(&spi4_config);
    spi_setup_config(&spi5_config);

    // Configure nSS pins
    gpio_init_pins(group_ss_pins, group_count);
    gpio_init_pins(disable_cs_pins, disable_cs_pin_count);
}

void spi_register_completion_handler(spi_completion_handler *handler)
{
    completion_handler = handler;
}

void spi_select_group(int group)
{
    assert(group <= group_count);
    const gpio_pin *grp = &group_ss_pins[group];

    gpio_clear(grp->gp_port, grp->gp_pin);
}

void spi_deselect_group(int group)
{
    assert(group <= group_count);
    const gpio_pin *grp = &group_ss_pins[group];

    gpio_set(grp->gp_port, grp->gp_pin);
}

void spi_start_transfer(int            spi,
                        uint8_t const *tx_buf,
                        uint8_t       *rx_buf,
                        size_t         count)
{
    assert(spi < SPI_BUS_RANGE);
    const spi_config *config = config_map[spi];
    assert(config);
    uint32_t base       = config->sc_reg_base;
    uint32_t rx_dma     = config->sc_rx_dma.dc_dma;
    uint8_t  rx_stream  = config->sc_rx_dma.dc_stream;
    uint32_t rx_channel = config->sc_rx_dma.dc_channel;
    uint32_t tx_dma     = config->sc_tx_dma.dc_dma;
    uint8_t  tx_stream  = config->sc_tx_dma.dc_stream;
    uint32_t tx_channel = config->sc_tx_dma.dc_channel;

    mark_bus_active(spi);
    
    //  1. Clear SxCR_EN.  Wait until SxCR_EN == 0.
    dma_stream_reset(rx_dma, rx_stream);
    while (DMA_SCR(rx_dma, rx_stream) & DMA_SxCR_EN)
        continue;

    //  2. Set peripheral port address register, SxPAR.
    dma_set_peripheral_address(rx_dma, rx_stream, (uint32_t)&SPI_DR(base));

    //  3. Set memory address register, SxMA0R.
    dma_set_memory_address(rx_dma, rx_stream, (uint32_t)rx_buf);

    //  4. Set number of data items, SxNDTR
    dma_set_number_of_data(rx_dma, rx_stream, count);

    //  5. Set the dma channel using SxCR.CHSEL[2:0].
    uint32_t rx_chsel = (uint32_t)rx_channel << DMA_SxCR_CHSEL_SHIFT;
    dma_channel_select(rx_dma, rx_stream, rx_chsel);

    //  6. Set SxCR.PFCTRL.
    dma_set_dma_flow_control(rx_dma, rx_stream);

    //  7. Set the stream priority.
    dma_set_priority(rx_dma, rx_stream, DMA_SxCR_PL_LOW);

    //  8. Set FIFO mode: disabled.
    dma_enable_direct_mode(rx_dma, rx_stream);

    //  9. Set data transfer direction,
    //         peripheral and memory increment/fixed mode,
    //         single or burst transactions,
    //         peripheral and memory data widths,
    //         circular mode,
    //         double buffer mode,
    //         and interrupts
    //     in the SxCR register.
    dma_disable_peripheral_increment_mode(rx_dma, rx_stream);
    dma_enable_memory_increment_mode(rx_dma, rx_stream);
    dma_set_peripheral_burst(rx_dma, rx_stream, DMA_SxCR_PBURST_SINGLE);
    dma_set_memory_burst(rx_dma, rx_stream, DMA_SxCR_MBURST_SINGLE);
    dma_set_peripheral_size(rx_dma, rx_stream, DMA_SxCR_PSIZE_8BIT);
    dma_set_memory_size(rx_dma, rx_stream, DMA_SxCR_MSIZE_8BIT);
    dma_set_transfer_mode(rx_dma, rx_stream, DMA_SxCR_DIR_PERIPHERAL_TO_MEM);
    dma_disable_double_buffer_mode(rx_dma, rx_stream);
    dma_disable_transfer_error_interrupt(rx_dma, rx_stream);
    dma_disable_half_transfer_interrupt(rx_dma, rx_stream);
    dma_enable_transfer_complete_interrupt(rx_dma, rx_stream);
    dma_disable_direct_mode_error_interrupt(rx_dma, rx_stream);
    dma_disable_fifo_error_interrupt(rx_dma, rx_stream);

    // 10. Set SxCR_EN.
    dma_enable_stream(rx_dma, rx_stream);

    //  1. Clear SxCR_EN.  Wait until SxCR_EN == 0.
    dma_stream_reset(tx_dma, tx_stream);
    while (DMA_SCR(tx_dma, tx_stream) & DMA_SxCR_EN)
        continue;

    //  2. Set peripheral port address register, SxPAR.
    dma_set_peripheral_address(tx_dma, tx_stream, (uint32_t)&SPI_DR(base));

    //  3. Set memory address register, SxMA0R.
    dma_set_memory_address(tx_dma, tx_stream, (uint32_t)tx_buf);

    //  4. Set number of data items, SxNDTR
    dma_set_number_of_data(tx_dma, tx_stream, count);

    //  5. Set the dma channel using SxCR.CHSEL[2:0].
    uint32_t tx_chsel = (uint32_t)tx_channel << DMA_SxCR_CHSEL_SHIFT;
    dma_channel_select(tx_dma, tx_stream, tx_chsel);

    //  6. Set SxCR.PFCTRL.
    dma_set_dma_flow_control(tx_dma, tx_stream);

    //  7. Set the stream priority.
    dma_set_priority(tx_dma, tx_stream, DMA_SxCR_PL_LOW);

    //  8. Set FIFO mode: disabled.
    dma_enable_direct_mode(tx_dma, tx_stream);

    //  9. Set data transfer direction,
    //         peripheral and memory increment/fixed mode,
    //         single or burst transactions,
    //         peripheral and memory data widths,
    //         circular mode,
    //         double buffer mode,
    //         and interrupts
    //     in the SxCR register.
    dma_disable_peripheral_increment_mode(tx_dma, tx_stream);
    dma_enable_memory_increment_mode(tx_dma, tx_stream);
    dma_set_peripheral_burst(tx_dma, tx_stream, DMA_SxCR_PBURST_SINGLE);
    dma_set_memory_burst(tx_dma, tx_stream, DMA_SxCR_MBURST_SINGLE);
    dma_set_peripheral_size(tx_dma, tx_stream, DMA_SxCR_PSIZE_8BIT);
    dma_set_memory_size(tx_dma, tx_stream, DMA_SxCR_MSIZE_8BIT);
    dma_set_transfer_mode(tx_dma, tx_stream, DMA_SxCR_DIR_MEM_TO_PERIPHERAL);
    dma_disable_double_buffer_mode(tx_dma, tx_stream);
    dma_disable_transfer_error_interrupt(tx_dma, tx_stream);
    dma_disable_half_transfer_interrupt(tx_dma, tx_stream);
    dma_disable_transfer_complete_interrupt(tx_dma, tx_stream);
    dma_disable_direct_mode_error_interrupt(tx_dma, tx_stream);
    dma_disable_fifo_error_interrupt(tx_dma, tx_stream);

    // 10. Set SxCR_EN.
    dma_enable_stream(tx_dma, tx_stream);

    spi_enable(config->sc_reg_base);
}

void spi_finish_transfer(int spi)
{
    assert(spi <= 6);
    const spi_config *config = config_map[spi];
    assert(config);
    uint32_t base      = config->sc_reg_base;
    uint32_t rx_dma    = config->sc_rx_dma.dc_dma;
    uint8_t  rx_stream = config->sc_rx_dma.dc_stream;
    uint32_t tx_dma    = config->sc_tx_dma.dc_dma;
    uint8_t  tx_stream = config->sc_tx_dma.dc_stream;

    // Wait for I/O to drain.  See sections 28.3.8, Disabling the SPI,
    // and 28.3.9, SPI communication using DMA.
    while (!dma_get_interrupt_flag(tx_dma, tx_stream, DMA_TCIF))
        continue;

    while (!(SPI_SR(base) & SPI_SR_TXE))
        continue;
    while (SPI_SR(base) & SPI_SR_BSY)
        continue;

    // Disable DMA first, then SPI.
    DMA_SCR(tx_dma, tx_stream) &= ~DMA_SxCR_EN;
    while (DMA_SCR(tx_dma, tx_stream) & DMA_SxCR_EN)
        continue;

    DMA_SCR(rx_dma, rx_stream) &= ~DMA_SxCR_EN;
    while (DMA_SCR(rx_dma, rx_stream) & DMA_SxCR_EN)
        continue;

    spi_disable(base);
}
