kbob/MinimumViableSynth/Firmware/Master/src/anim.h

#ifndef ANIM_included
#define ANIM_included

#include <stddef.h>
#include <stdint.h>

typedef uint32_t packed_RGB;

extern void anim_update(uint32_t msec);

extern packed_RGB anim_module_color(size_t module_index);
extern packed_RGB anim_knob_color(size_t module_index, size_t knob_index);
extern uint8_t    anim_choice_brightness(size_t module_index);
extern uint8_t    anim_assign_brightness(size_t module_index);

#endif /* !ANIM_included */
